Xinyuan-LilyGO/T-QT/data/t-qt-pro-2.jpg

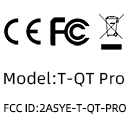
data/t-qt-pro-2.jpg
