Xinyuan-LilyGO/T-QT/examples/LVGL_Factory/clock_hour_img.c

#if defined(LV_LVGL_H_INCLUDE_SIMPLE)
#include "lvgl.h"
#else
#include "lvgl.h"
#endif


#ifndef LV_ATTRIBUTE_MEM_ALIGN
#define LV_ATTRIBUTE_MEM_ALIGN
#endif

#ifndef LV_ATTRIBUTE_IMG_CLOCK_HOUR_IMG
#define LV_ATTRIBUTE_IMG_CLOCK_HOUR_IMG
#endif

const LV_ATTRIBUTE_MEM_ALIGN LV_ATTRIBUTE_LARGE_CONST LV_ATTRIBUTE_IMG_CLOCK_HOUR_IMG uint8_t clock_hour_img_map[] = {
#if LV_COLOR_DEPTH == 1 || LV_COLOR_DEPTH == 8
  /*Pixel format: Alpha 8 bit, Red: 3 bit, Green: 3 bit, Blue: 2 bit*/
  0x00, 0x00, 0x00, 0x00, 0xff, 0x7f, 0x00, 0x00, 0x00, 0x00, 
  0x00, 0x00, 0xff, 0xff, 0xff, 0xff, 0xff, 0xbe, 0x00, 0x00, 
  0x00, 0x00, 0xff, 0xff, 0xff, 0xff, 0xff, 0xe5, 0x00, 0x00, 
  0x00, 0x00, 0xff, 0xff, 0xff, 0xff, 0xff, 0xe0, 0x00, 0x00, 
  0x00, 0x00, 0xff, 0xff, 0xff, 0xff, 0xff, 0xe0, 0x00, 0x00, 
  0x00, 0x00, 0xff, 0xff, 0xff, 0xff, 0xff, 0xe0, 0x00, 0x00, 
  0x00, 0x00, 0xff, 0xff, 0xff, 0xff, 0xff, 0xe0, 0x00, 0x00, 
  0x00, 0x00, 0xff, 0xff, 0xff, 0xff, 0xff, 0xde, 0x00, 0x00, 
  0x00, 0x00, 0xff, 0xff, 0xff, 0xff, 0xff, 0xdd, 0x00, 0x00, 
  0x00, 0x00, 0xff, 0xff, 0xff, 0xff, 0xff, 0xdd, 0x00, 0x00, 
  0x00, 0x00, 0xff, 0xff, 0xff, 0xff, 0xff, 0xdd, 0x00, 0x00, 
  0x00, 0x00, 0xff, 0xff, 0xff, 0xff, 0xff, 0xdd, 0x00, 0x00, 
  0x00, 0x00, 0xff, 0xff, 0xff, 0xff, 0xff, 0xdd, 0x00, 0x00, 
  0x00, 0x00, 0xff, 0xff, 0xff, 0xff, 0xff, 0xdd, 0x00, 0x00, 
  0x00, 0x00, 0xff, 0xff, 0xff, 0xff, 0xff, 0xdd, 0x00, 0x00, 
  0x00, 0x00, 0xff, 0xff, 0xff, 0xff, 0xff, 0xdd, 0x00, 0x00, 
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
  0x00, 0x00, 0x00, 0x00, 0x00, 0x00, 0x00, 0x00, 0xff, 0xff, 0xff, 0xff, 0x00, 0x00, 0x00, 0x00, 0x00, 0x00, 0x00, 0x00, 
  0x00, 0x00, 0x00, 0x00, 0x00, 0x00, 0x00, 0x00, 0xff, 0xff, 0xff, 0xff, 0x00, 0x00, 0x00, 0x00, 0x00, 0x00, 0x00, 0x00, 
  0x00, 0x00, 0x00, 0x00, 0x00, 0x00, 0x00, 0x00, 0xff, 0xff, 0xff, 0xa3, 0x00, 0x00, 0x00, 0x00, 0x00, 0x00, 0x00, 0x00, 
#endif
};

const lv_img_dsc_t clock_hour_img = {
  .header.cf = LV_IMG_CF_TRUE_COLOR_ALPHA,
  .header.always_zero = 0,
  .header.reserved = 0,
  .header.w = 5,
  .header.h = 30,
  .data_size = 150 * LV_IMG_PX_SIZE_ALPHA_BYTE,
  .data = clock_hour_img_map,
};
