Xinyuan-LilyGO/T-QT/examples/LVGL_Factory/clock_sec_img.c

#if defined(LV_LVGL_H_INCLUDE_SIMPLE)
#include "lvgl.h"
#else
#include "lvgl.h"
#endif


#ifndef LV_ATTRIBUTE_MEM_ALIGN
#define LV_ATTRIBUTE_MEM_ALIGN
#endif

#ifndef LV_ATTRIBUTE_IMG_CLOCK_SEC_IMG
#define LV_ATTRIBUTE_IMG_CLOCK_SEC_IMG
#endif

const LV_ATTRIBUTE_MEM_ALIGN LV_ATTRIBUTE_LARGE_CONST LV_ATTRIBUTE_IMG_CLOCK_SEC_IMG uint8_t clock_sec_img_map[] = {
#if LV_COLOR_DEPTH == 1 || LV_COLOR_DEPTH == 8
  /*Pixel format: Alpha 8 bit, Red: 3 bit, Green: 3 bit, Blue: 2 bit*/
  0x00, 0x00, 0x00, 0x00, 0xff, 0x02, 0xfa, 0x55, 0xfa, 0x5a, 0xff, 0x06, 0x00, 0x00, 0x00, 0x00, 
  0x00, 0x00, 0x00, 0x00, 0xff, 0x04, 0xf4, 0xee, 0xf4, 0xfc, 0xff, 0x11, 0x00, 0x00, 0x00, 0x00, 
  0x00, 0x00, 0x00, 0x00, 0xff, 0x04, 0xf5, 0xe1, 0xf4, 0xef, 0xff, 0x11, 0x00, 0x00, 0x00, 0x00, 
  0x00, 0x00, 0x00, 0x00, 0xff, 0x04, 0xf5, 0xe1, 0xf4, 0xf0, 0xff, 0x12, 0x00, 0x00, 0x00, 0x00, 
  0x00, 0x00, 0x00, 0x00, 0xff, 0x03, 0xf5, 0xe0, 0xf4, 0xf1, 0xff, 0x12, 0x00, 0x00, 0x00, 0x00, 
  0x00, 0x00, 0x00, 0x00, 0xff, 0x03, 0xf5, 0xde, 0xf4, 0xf1, 0xff, 0x12, 0x00, 0x00, 0x00, 0x00, 
  0x00, 0x00, 0x00, 0x00, 0xff, 0x03, 0xf5, 0xde, 0xf4, 0xf1, 0xff, 0x12, 0x00, 0x00, 0x00, 0x00, 
  0x00, 0x00, 0x00, 0x00, 0xff, 0x03, 0xf5, 0xde, 0xf4, 0xf2, 0xff, 0x13, 0x00, 0x00, 0x00, 0x00, 
  0x00, 0x00, 0x00, 0x00, 0xff, 0x03, 0xf5, 0xdd, 0xf4, 0xf3, 0xff, 0x15, 0x00, 0x00, 0x00, 0x00, 
  0x00, 0x00, 0x00, 0x00, 0xff, 0x03, 0xf5, 0xdc, 0xf4, 0xf3, 0xff, 0x15, 0x00, 0x00, 0x00, 0x00, 
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
#endif
};

const lv_img_dsc_t clock_sec_img = {
  .header.cf = LV_IMG_CF_TRUE_COLOR_ALPHA,
  .header.always_zero = 0,
  .header.reserved = 0,
  .header.w = 8,
  .header.h = 61,
  .data_size = 488 * LV_IMG_PX_SIZE_ALPHA_BYTE,
  .data = clock_sec_img_map,
};
