Xinyuan-LilyGO/T-QT/examples/LVGL_Factory/duck_gif.c

#if defined(LV_LVGL_H_INCLUDE_SIMPLE)
#include "lvgl.h"
#else
#include "lvgl.h"
#endif


#ifndef LV_ATTRIBUTE_MEM_ALIGN
#define LV_ATTRIBUTE_MEM_ALIGN
#endif

#ifndef LV_ATTRIBUTE_IMG_duck_GIF
#define LV_ATTRIBUTE_IMG_duck_GIF
#endif

const LV_ATTRIBUTE_MEM_ALIGN LV_ATTRIBUTE_LARGE_CONST LV_ATTRIBUTE_IMG_duck_GIF uint8_t duck_gif_map[] = {
    0x47, 0x49, 0x46, 0x38, 0x39, 0x61, 0x80, 0x00, 0x80, 0x00, 0xf7, 0x00, 0x00, 
    0x00, 0x00, 0x00, 0xff, 0xff, 0xff, 0x66, 0xcc, 0x66, 0x33, 0x66, 0x33, 0x08, 
    0x02, 0x08, 0x03, 0x01, 0x03, 0x01, 0x01, 0x12, 0x01, 0x01, 0x07, 0x01, 0x01, 
    0x03, 0x35, 0x35, 0x36, 0x4f, 0x4f, 0x50, 0xfd, 0xfd, 0xff, 0x9b, 0x9b, 0x9c, 
    0x05, 0x08, 0x1f, 0x57, 0x5a, 0x71, 0xe3, 0xe5, 0xf4, 0x0e, 0x11, 0x23, 0x2b, 
    0x2f, 0x47, 0x19, 0x1e, 0x37, 0x25, 0x29, 0x3d, 0x71, 0x77, 0x91, 0x87, 0x91, 
    0xa4, 0xb7, 0xc0, 0xcb, 0xc7, 0xd0, 0xda, 0xfb, 0xfd, 0xff, 0x01, 0x04, 0x04, 
    0xf2, 0xff, 0xff, 0x02, 0x0e, 0x0c, 0x01, 0x09, 0x07, 0x03, 0x16, 0x10, 0x04, 
    0x23, 0x16, 0x07, 0x35, 0x20, 0x0e, 0x52, 0x30, 0x23, 0x63, 0x35, 0x37, 0x95, 
    0x4f, 0x31, 0x71, 0x3b, 0x2d, 0x67, 0x35, 0x25, 0x53, 0x2b, 0x4c, 0xa4, 0x54, 
    0x5b, 0xc3, 0x63, 0x2b, 0x58, 0x2d, 0x2f, 0x5f, 0x31, 0x66, 0xd2, 0x6a, 0x77, 
    0xf1, 0x79, 0x6f, 0xe1, 0x71, 0x6b, 0xd9, 0x6d, 0x65, 0xcd, 0x67, 0x63, 0xc9, 
    0x65, 0x37, 0x6f, 0x39, 0x33, 0x67, 0x35, 0x7b, 0xf7, 0x7d, 0x77, 0xef, 0x79, 
    0x73, 0xe7, 0x75, 0x6f, 0xdf, 0x71, 0x6b, 0xd7, 0x6d, 0x69, 0xd3, 0x6b, 0x67, 
    0xcf, 0x69, 0x65, 0xcb, 0x67, 0x01, 0x03, 0x01, 0x03, 0x07, 0x03, 0x27, 0x51, 
    0x27, 0x65, 0xcf, 0x65, 0x31, 0x65, 0x31, 0x2f, 0x61, 0x2f, 0x77, 0xf1, 0x77, 
    0x73, 0xe9, 0x73, 0x6f, 0xe1, 0x6f, 0x6d, 0xdd, 0x6e, 0x6b, 0xd9, 0x6b, 0x67, 
    0xd1, 0x67, 0x65, 0xcd, 0x65, 0x33, 0x67, 0x33, 0x2f, 0x5f, 0x2f, 0x21, 0x43, 
    0x21, 0x69, 0xd3, 0x69, 0x67, 0xcf, 0x67, 0x65, 0xcb, 0x65, 0x63, 0xc7, 0x63, 
    0x7d, 0xfa, 0x7d, 0x7b, 0xf6, 0x7b, 0x79, 0xf2, 0x79, 0x77, 0xee, 0x77, 0x75, 
    0xea, 0x75, 0x73, 0xe6, 0x73, 0x71, 0xe2, 0x71, 0x6f, 0xde, 0x6f, 0x6d, 0xda, 
    0x6d, 0x6b, 0xd6, 0x6b, 0x69, 0xd1, 0x69, 0x67, 0xcd, 0x67, 0x65, 0xc9, 0x65, 
    0x61, 0xc2, 0x61, 0x5f, 0xbd, 0x5f, 0x5a, 0xb3, 0x5a, 0x54, 0xa7, 0x54, 0x50, 
    0x9f, 0x50, 0x4e, 0x9c, 0x4e, 0x4c, 0x98, 0x4c, 0x4a, 0x93, 0x4a, 0x46, 0x8c, 
    0x46, 0x41, 0x82, 0x41, 0x3d, 0x7a, 0x3d, 0x3b, 0x76, 0x3b, 0x31, 0x62, 0x31, 
    0x2e, 0x5c, 0x2e, 0x2b, 0x56, 0x2b, 0x27, 0x4e, 0x27, 0x1a, 0x34, 0x1a, 0x16, 
    0x2c, 0x16, 0x12, 0x24, 0x12, 0x0b, 0x16, 0x0b, 0x07, 0x0e, 0x07, 0x80, 0xfe, 
    0x80, 0x7d, 0xf7, 0x7d, 0x7b, 0xf3, 0x7b, 0x79, 0xef, 0x79, 0x75, 0xe7, 0x75, 
    0x73, 0xe3, 0x73, 0x71, 0xdf, 0x71, 0x6f, 0xdb, 0x6f, 0x6d, 0xd7, 0x6d, 0x6b, 
    0xd3, 0x6b, 0x69, 0xcf, 0x69, 0x67, 0xcb, 0x67, 0x63, 0xc4, 0x63, 0x3f, 0x7d, 
    0x3f, 0x37, 0x6d, 0x37, 0x33, 0x65, 0x33, 0x2d, 0x59, 0x2d, 0x39, 0x70, 0x39, 
    0x35, 0x68, 0x35, 0x1e, 0x3b, 0x1e, 0x6b, 0xd1, 0x6b, 0x67, 0xc9, 0x67, 0x31, 
    0x5f, 0x31, 0x0f, 0x1d, 0x0f, 0x89, 0xff, 0x8a, 0x2d, 0x53, 0x2d, 0x49, 0x60, 
    0x49, 0x06, 0x07, 0x06, 0xfd, 0xff, 0xfd, 0x7d, 0xf8, 0x7b, 0x79, 0xf1, 0x77, 
    0x75, 0xe9, 0x73, 0x71, 0xe1, 0x6f, 0x6d, 0xd9, 0x6b, 0x6a, 0xd5, 0x69, 0x69, 
    0xd1, 0x67, 0x67, 0xcd, 0x65, 0x3a, 0x73, 0x39, 0x38, 0x6f, 0x37, 0x36, 0x6b, 
    0x35, 0x2a, 0x53, 0x29, 0x25, 0x49, 0x24, 0x79, 0xef, 0x77, 0x75, 0xe7, 0x73, 
    0x71, 0xdf, 0x6f, 0x6d, 0xd7, 0x6b, 0x6b, 0xd3, 0x69, 0x69, 0xcf, 0x67, 0x67, 
    0xcb, 0x65, 0x65, 0xc7, 0x63, 0x5d, 0xb9, 0x5c, 0x57, 0xad, 0x56, 0x52, 0xa3, 
    0x51, 0x6b, 0xd1, 0x69, 0x67, 0xc9, 0x65, 0x61, 0xbf, 0x60, 0x44, 0x86, 0x43, 
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
};

const lv_img_dsc_t duck_gif = {
  .header.cf = LV_IMG_CF_RAW,
  .header.always_zero = 0,
  .header.reserved = 0,
  .header.w = 0,
  .header.h = 0,
  .data_size = 48007,
  .data = duck_gif_map,
};
