Xinyuan-LilyGO/T-QT/extras/GC9A01_Rotation.h

// This is the command sequence that rotates the GC9A01 driver coordinate frame

  rotation = m % 4;

  writecommand(TFT_MADCTL);
  switch (rotation) {
    case 0: // Portrait
      writedata(TFT_MAD_COLOR_ORDER);
      _width  = _init_width;
      _height = _init_height;
#ifdef CGRAM_OFFSET
      if (_init_width == 128)
      {
        colstart = 2;
        rowstart = 1;
      }
#endif    
      break;
    case 1: // Landscape (Portrait + 90)
      writedata(TFT_MAD_MX | TFT_MAD_MV | TFT_MAD_COLOR_ORDER);
      _width  = _init_height;
      _height = _init_width;
#ifdef CGRAM_OFFSET
      if (_init_width == 128)
      {
        colstart = 1;
        rowstart = 2;
      }
#endif
      break;
    case 2: // Inverter portrait
      writedata(TFT_MAD_MX | TFT_MAD_MY | TFT_MAD_COLOR_ORDER);
      _width  = _init_width;
      _height = _init_height;
#ifdef CGRAM_OFFSET
      if (_init_width == 128)
      {
        colstart = 2;
        rowstart = 1;
      }
#endif
      break;
    case 3: // Inverted landscape
      writedata(TFT_MAD_MV | TFT_MAD_MY | TFT_MAD_COLOR_ORDER);
      _width  = _init_height;
      _height = _init_width;
#ifdef CGRAM_OFFSET
      if (_init_width == 128)
      {
        colstart = 1;
        rowstart = 2;
      }
#endif
      break;
  }
